tamu-edu-students/CHO-MATE/SolidWorks/dispenserv3.SLDPRT

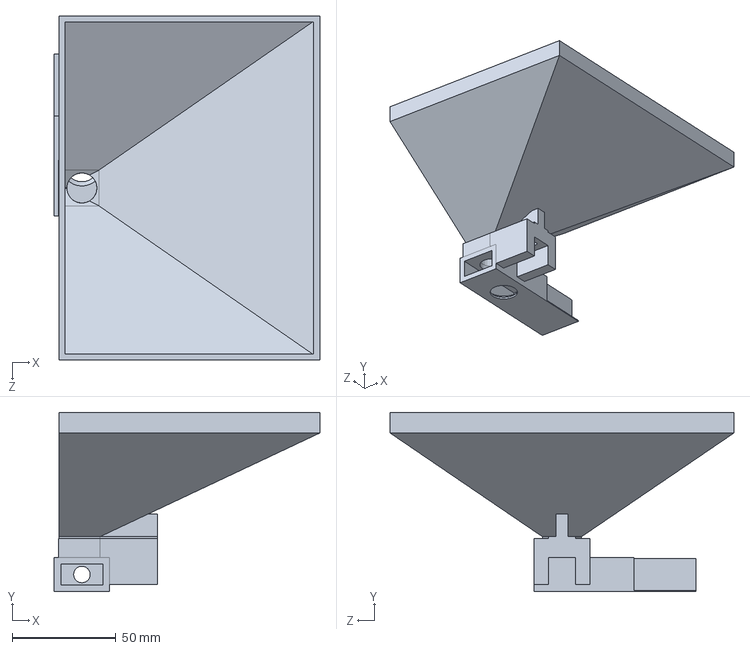
[picture p64: CAD file, 2022-11-30]
SolidWorks/dispenserv3.SLDPRT
128.2 x 86.6 x 166.0 mm
