tamu-edu-students/CHO-MATE/SolidWorks/actuator_mount.SLDPRT

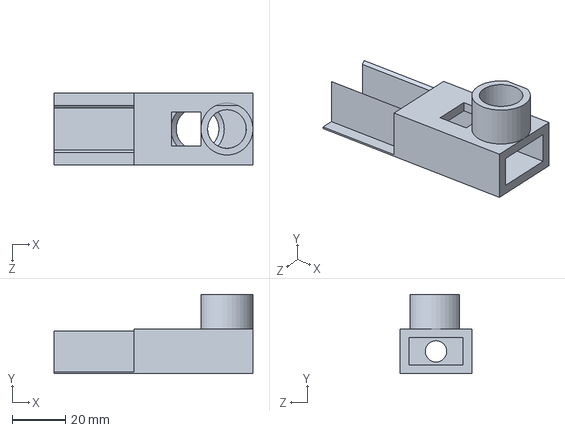
[picture p65: CAD file, 2022-11-30]
SolidWorks/actuator_mount.SLDPRT
74.5 x 29.6 x 26.8 mm
