tamu-edu-students/CHO-MATE/SolidWorks/pressure_sensor.SLDPRT

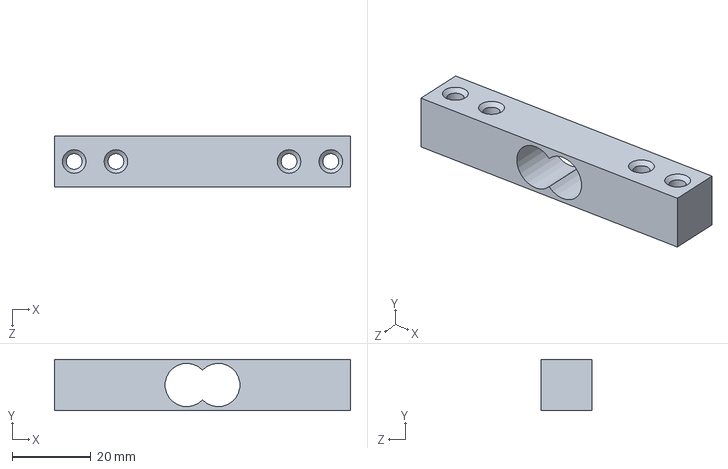
[picture p66: CAD file, 2022-11-30]
SolidWorks/pressure_sensor.SLDPRT
75.2 x 13.0 x 13.0 mm
