tamu-edu-students/CHO-MATE/SolidWorks/Tray_bottom.SLDPRT

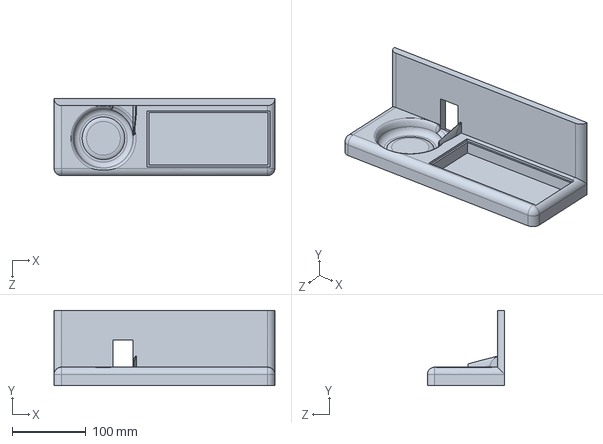
[picture p67: CAD file, 2022-11-30]
SolidWorks/Tray_bottom.SLDPRT
300.0 x 102.0 x 105.0 mm
