tamu-edu-students/CHO-MATE/SolidWorks/Bottom.SLDPRT

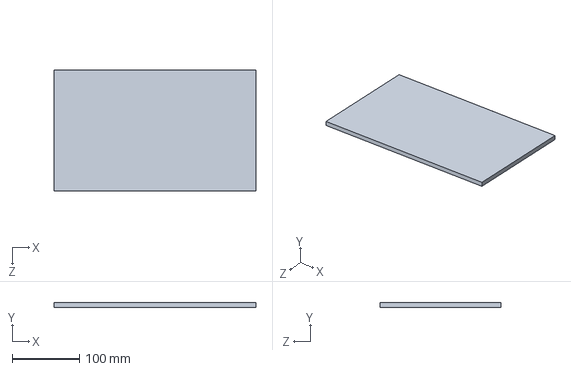
[picture p68: CAD file, 2022-11-30]
SolidWorks/Bottom.SLDPRT
300.0 x 7.00 x 180.0 mm
