tamu-edu-students/CHO-MATE/SolidWorks/Skittle Ramp.SLDPRT

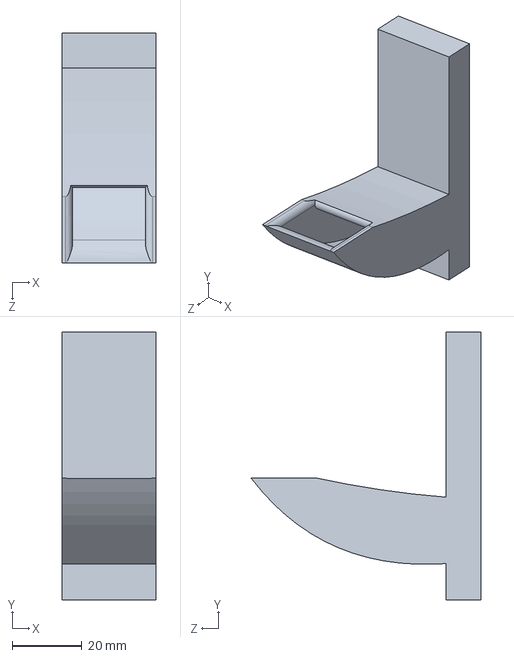
[picture p69: CAD file, 2022-11-30]
SolidWorks/Skittle Ramp.SLDPRT
27.0 x 77.0 x 66.0 mm
