tamu-edu-students/CHO-MATE/SolidWorks/Tray_Top_Left.SLDPRT

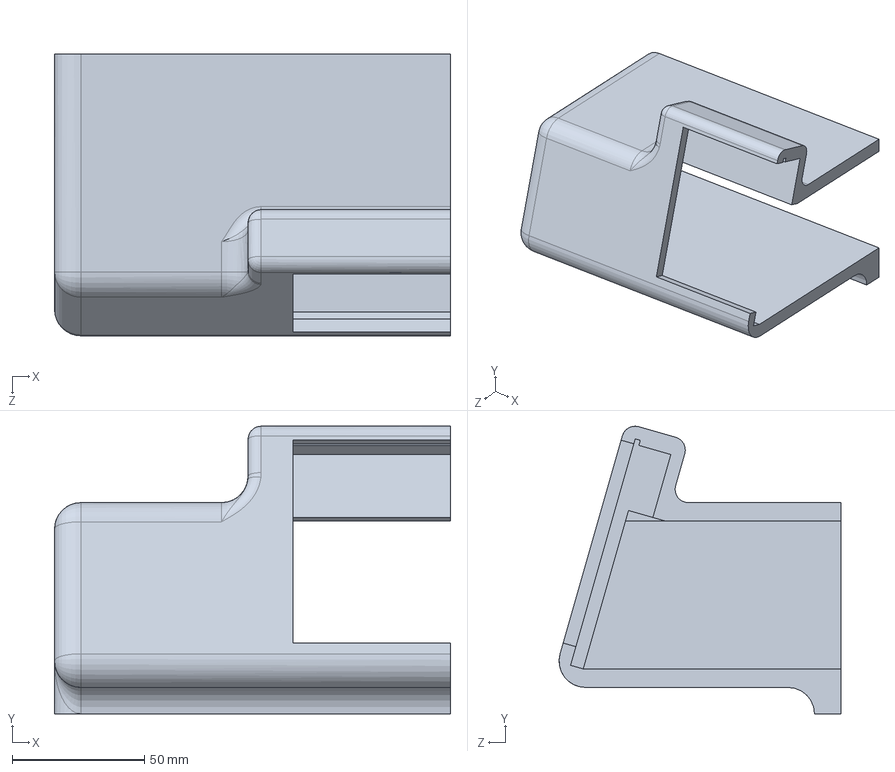
[picture p70: CAD file, 2022-11-30]
SolidWorks/Tray_Top_Left.SLDPRT
150.0 x 108.9 x 106.7 mm
