tamu-edu-students/CHO-MATE/SolidWorks/updated_funnel.SLDPRT

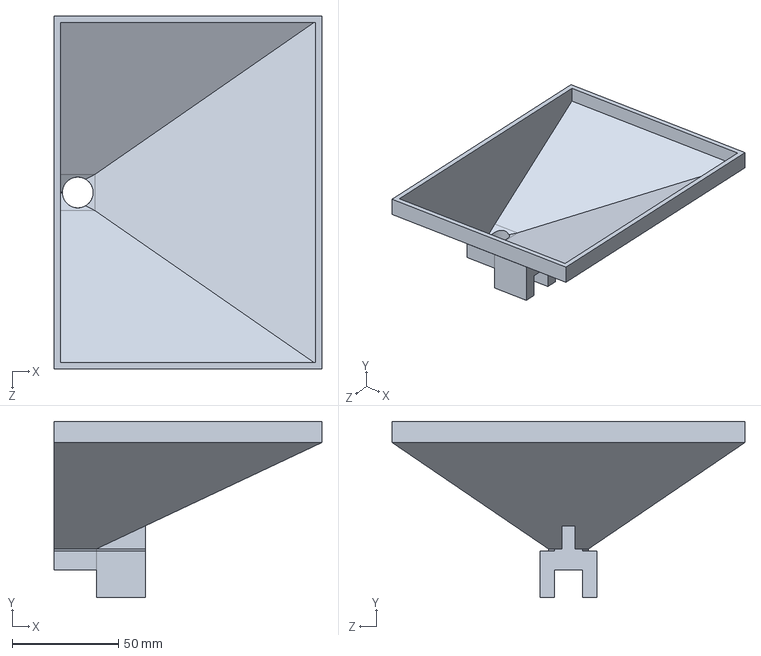
[picture p71: CAD file, 2022-11-30]
SolidWorks/updated_funnel.SLDPRT
126.0 x 83.0 x 166.0 mm
