tamu-edu-students/CHO-MATE/SolidWorks/Tray_Top.SLDPRT

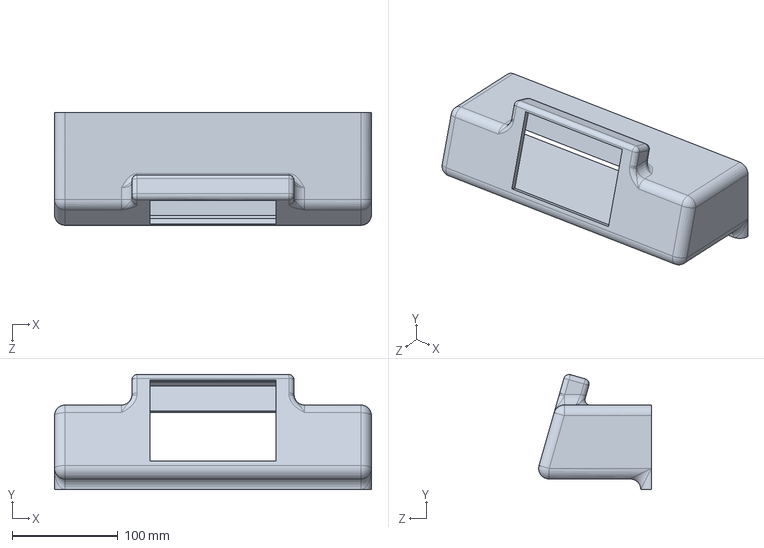
[picture p72: CAD file, 2022-11-30]
SolidWorks/Tray_Top.SLDPRT
300.0 x 108.9 x 106.7 mm
