tamu-edu-students/CHO-MATE/SolidWorks/Tray_bottom_right.SLDPRT

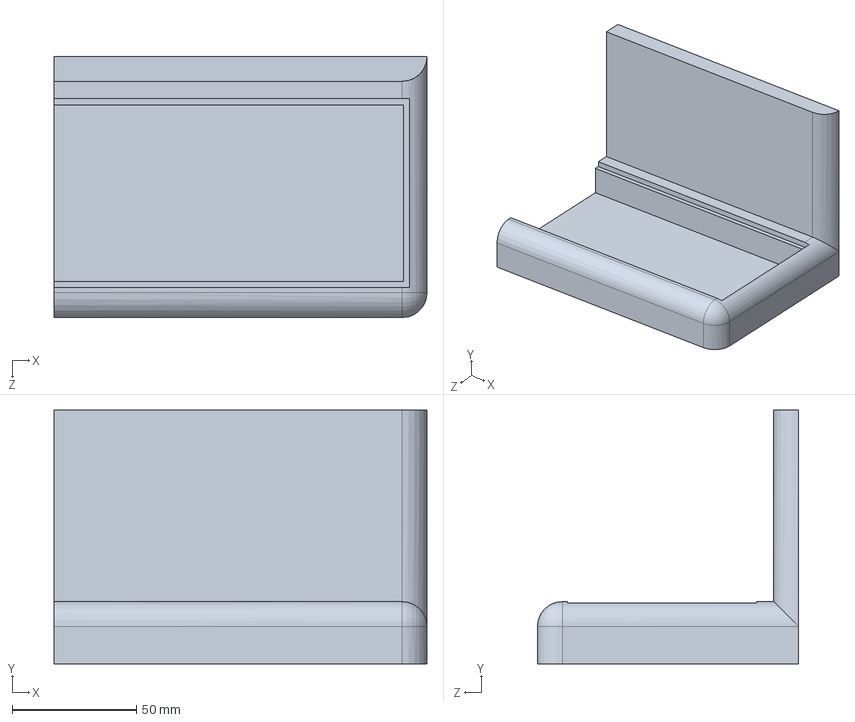
[picture p73: CAD file, 2022-11-30]
SolidWorks/Tray_bottom_right.SLDPRT
150.0 x 102.0 x 105.0 mm
