tamu-edu-students/CHO-MATE/SolidWorks/Skittle_container.SLDPRT

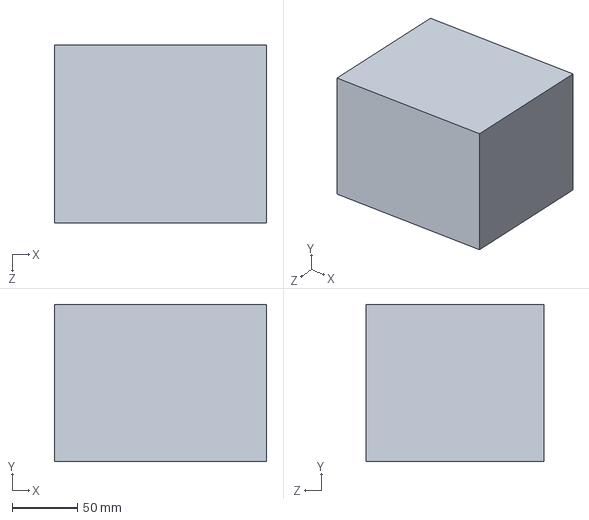
[picture p74: CAD file, 2022-11-30]
SolidWorks/Skittle_container.SLDPRT
162.0 x 120.0 x 136.0 mm
