tamu-edu-students/CHO-MATE/SolidWorks/skittle actuator.SLDPRT

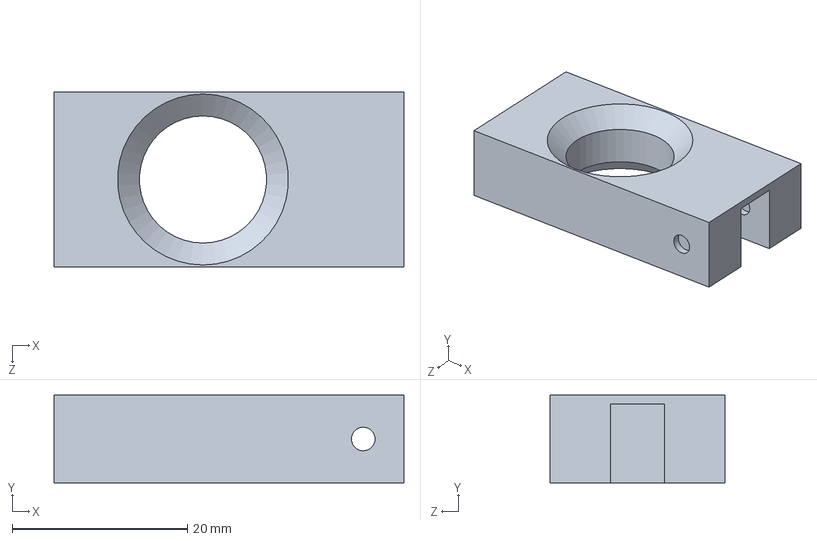
[picture p75: CAD file, 2022-11-30]
SolidWorks/skittle actuator.SLDPRT
39.9 x 10.0 x 20.0 mm
