tamu-edu-students/CHO-MATE/SolidWorks/Left.SLDPRT

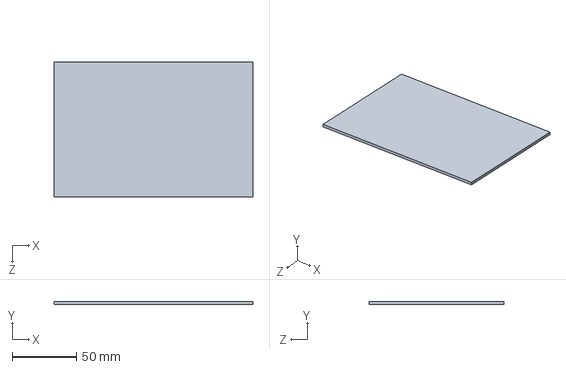
[picture p76: CAD file, 2022-11-30]
SolidWorks/Left.SLDPRT
154.7 x 2.38 x 104.7 mm
