tamu-edu-students/CHO-MATE/SolidWorks/Tray insert.SLDPRT

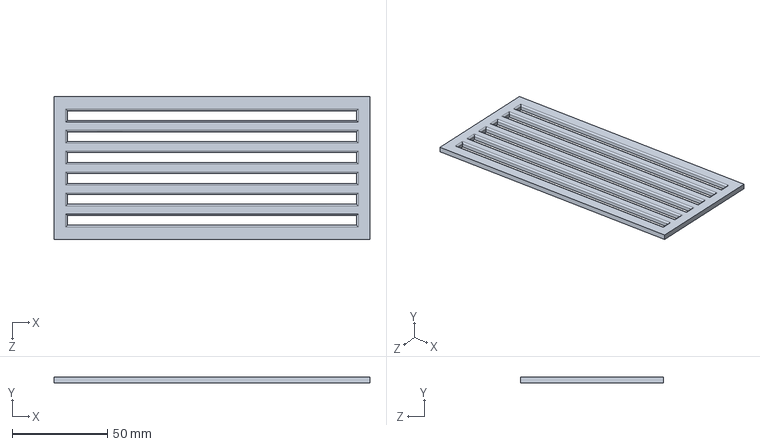
[picture p77: CAD file, 2022-11-30]
SolidWorks/Tray insert.SLDPRT
165.8 x 3.00 x 75.0 mm
