tamu-edu-students/CHO-MATE/SolidWorks/Right.SLDPRT

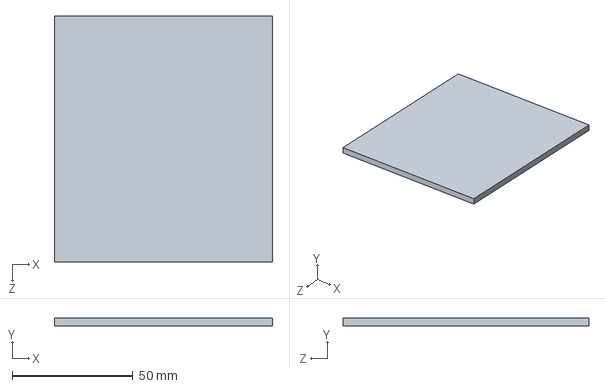
[picture p78: CAD file, 2022-11-30]
SolidWorks/Right.SLDPRT
90.3 x 3.40 x 101.8 mm
