tamu-edu-students/CHO-MATE/SolidWorks/Surge Protector.SLDPRT

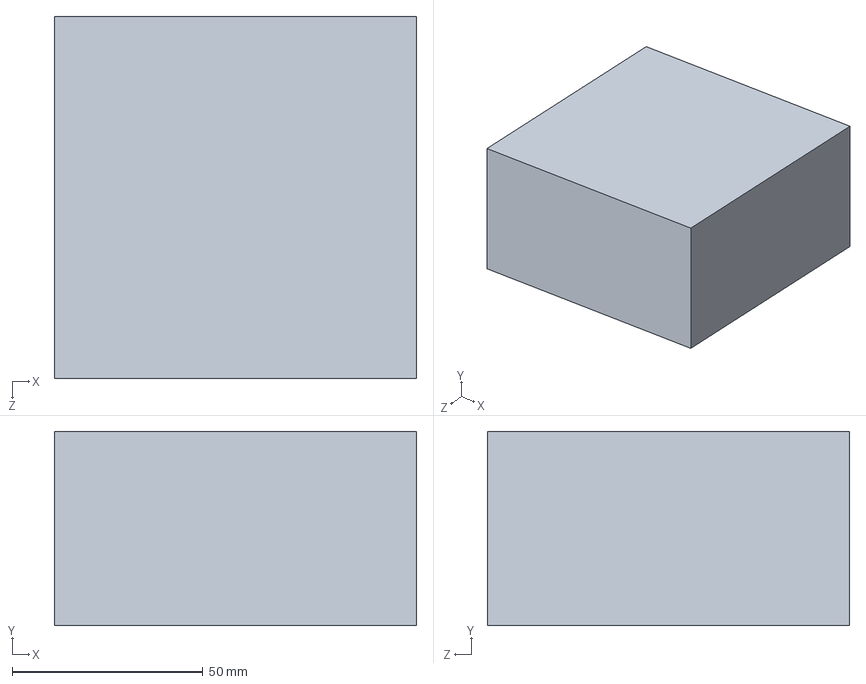
[picture p79: CAD file, 2022-11-30]
SolidWorks/Surge Protector.SLDPRT
95.0 x 51.0 x 95.0 mm
